quantcon/realistic-trc-retrofit/Photos/01.JPG

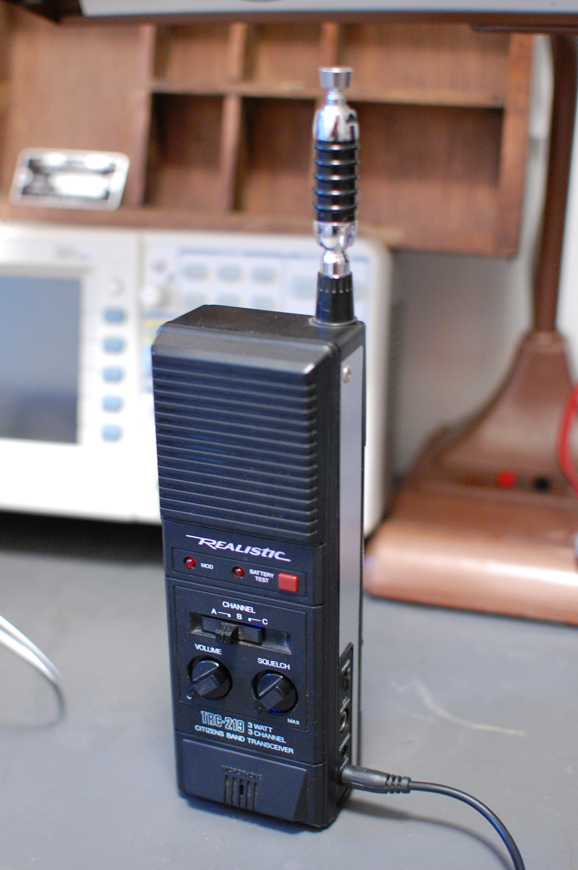
Photos/01.JPG
