quantcon/realistic-trc-retrofit/Photos/03.JPG

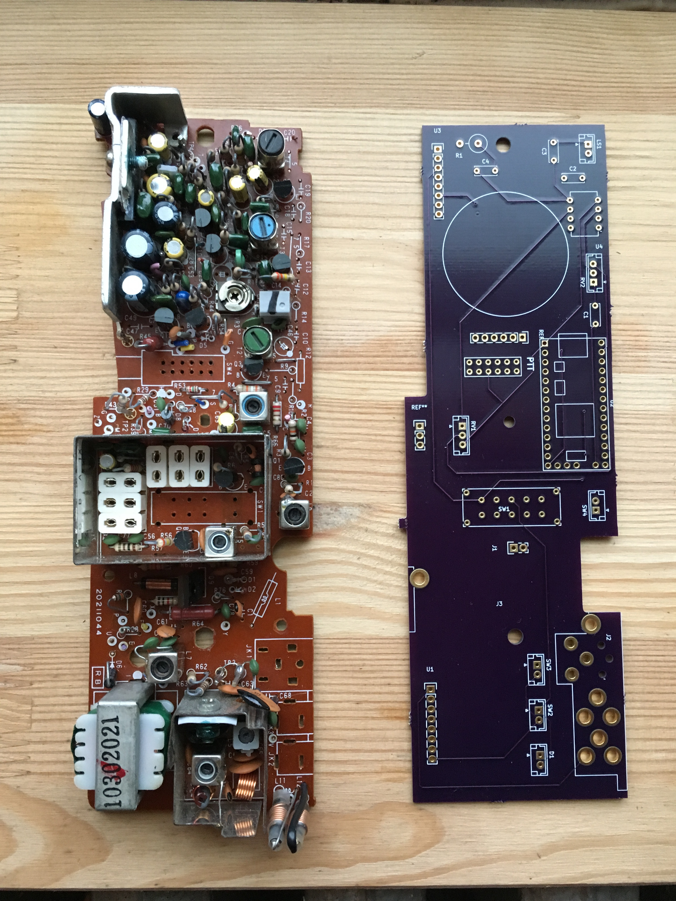
Photos/03.JPG
