quantcon/realistic-trc-retrofit/Photos/04.JPG

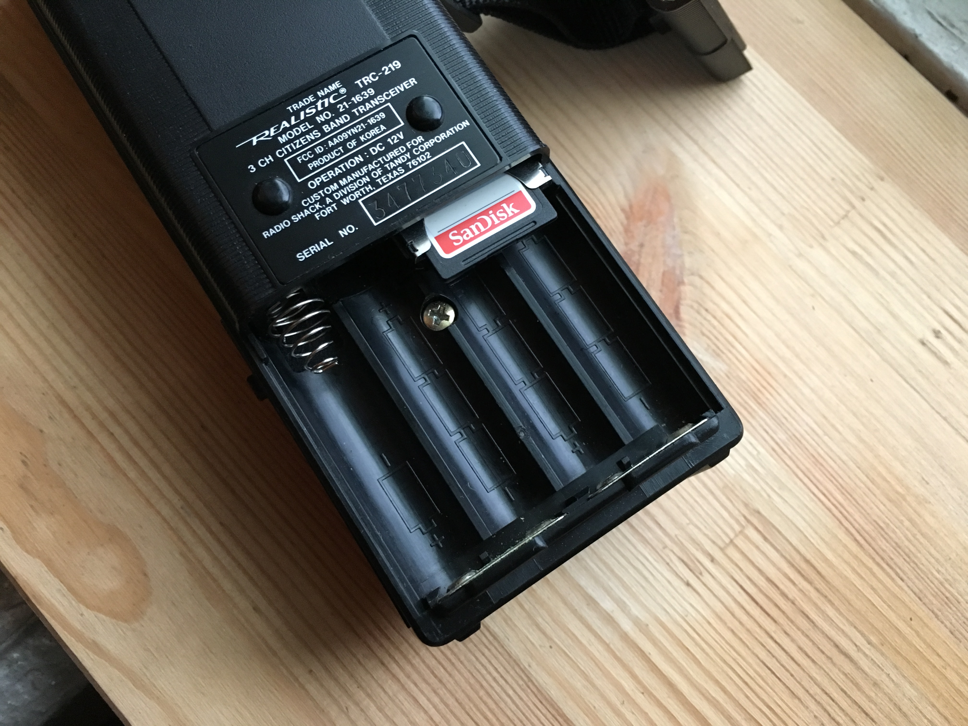
Photos/04.JPG
