quantcon/realistic-trc-retrofit/Photos/05.JPG

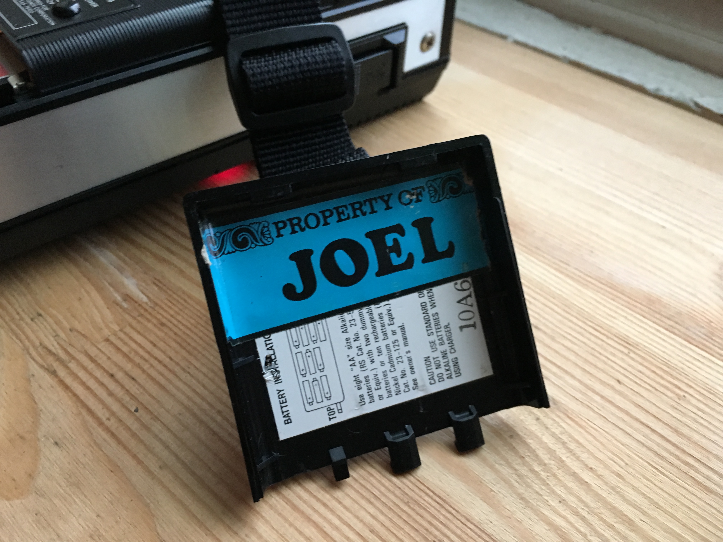
Photos/05.JPG
