quantcon/realistic-trc-retrofit/Photos/06.JPG

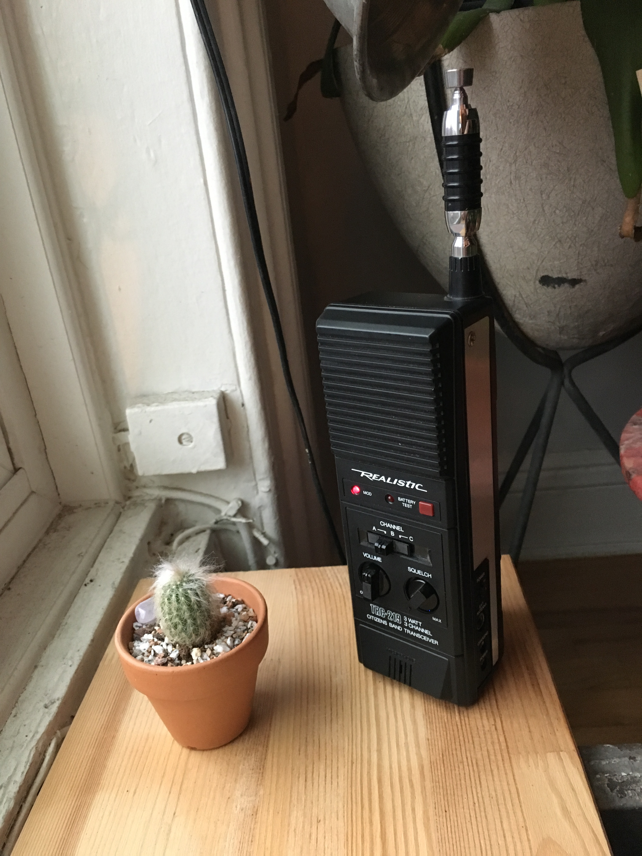
Photos/06.JPG
