quantcon/realistic-trc-retrofit/Photos/07.JPG

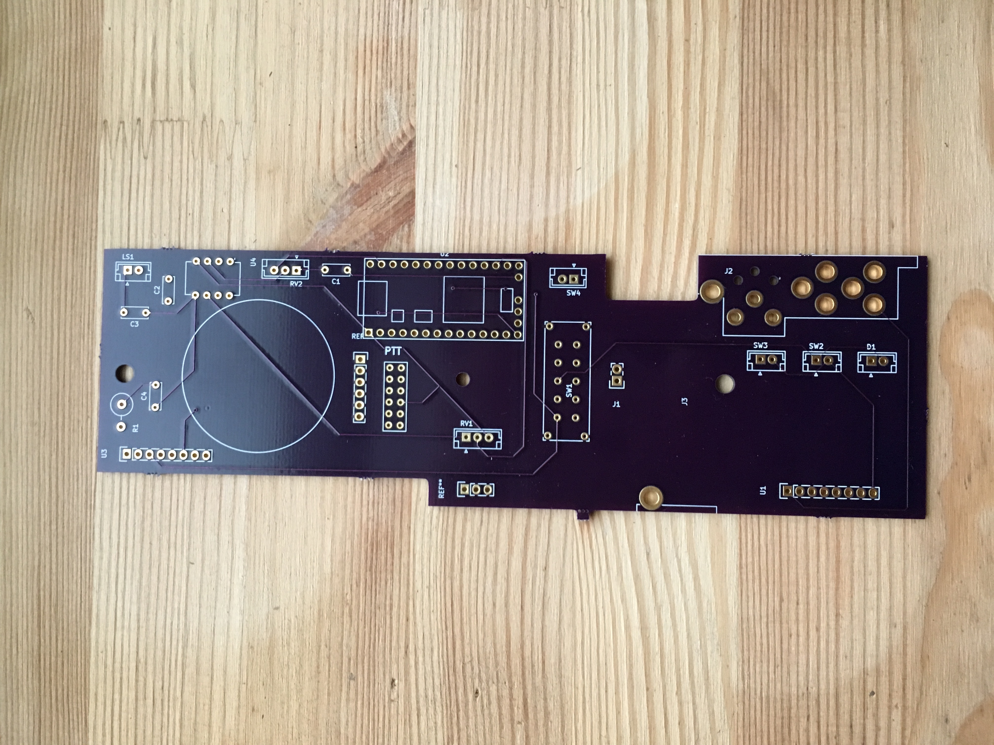
Photos/07.JPG
