quantcon/realistic-trc-retrofit/Photos/08.JPG

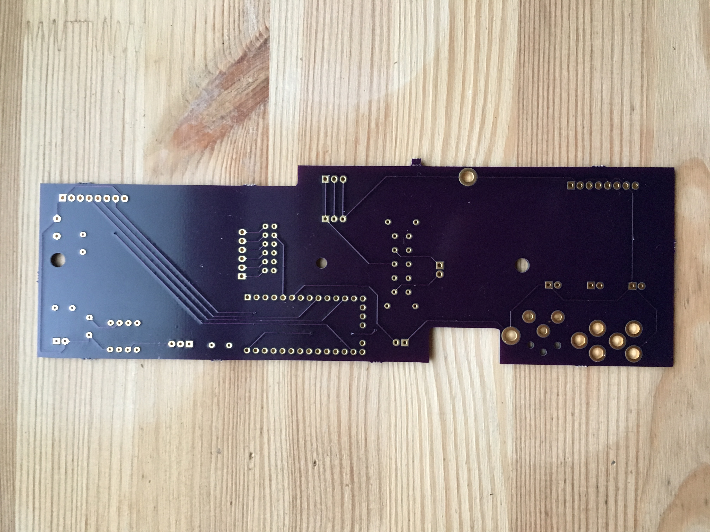
Photos/08.JPG
