quantcon/realistic-trc-retrofit/Photos/09.JPG

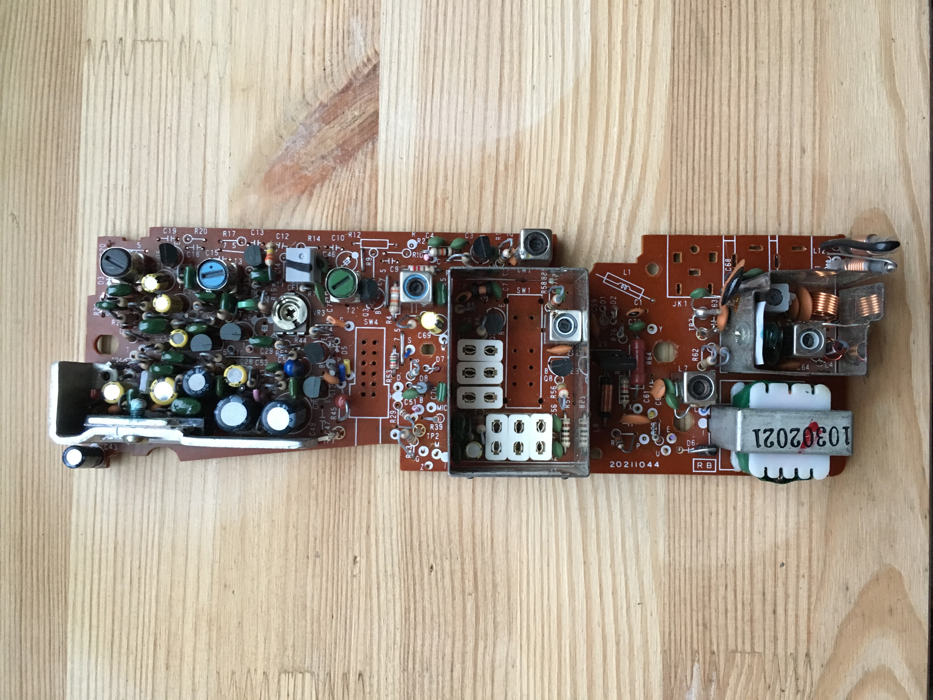
Photos/09.JPG
