quantcon/realistic-trc-retrofit/Photos/10.JPG

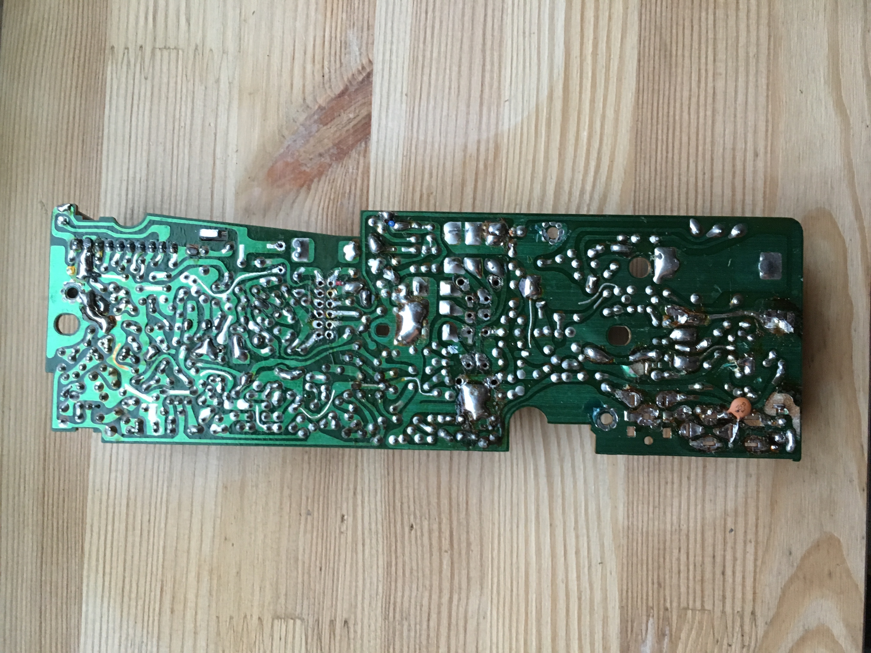
Photos/10.JPG
