quantcon/realistic-trc-retrofit/Photos/11.JPG

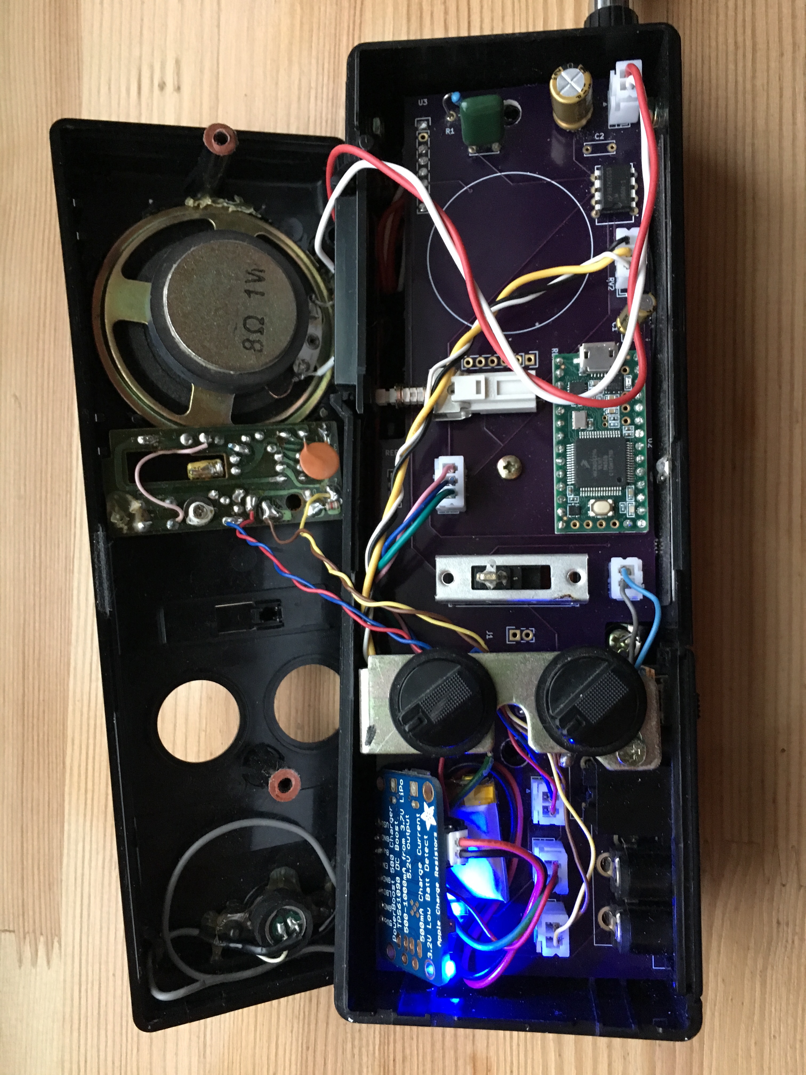
Photos/11.JPG
